marecl/Temperature-Station/Temperature-Station_DS3231/PCB/TermometryWiFi_MainBoard_57640_etch_silk_bottom.pdf

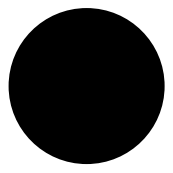
[picture p11: page 1]
