marecl/Temperature-Station/Temperature-Station_DS3231/PCB/TermometryWiFi_MainBoard_57640_etch_silk_bottom_mirror.pdf

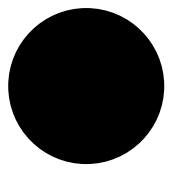
[picture p12: page 1]
