marecl/Temperature-Station/Temperature-Station_DS3231/PCB/TermometryWiFi_MainBoard_57640_etch_silk_top.pdf

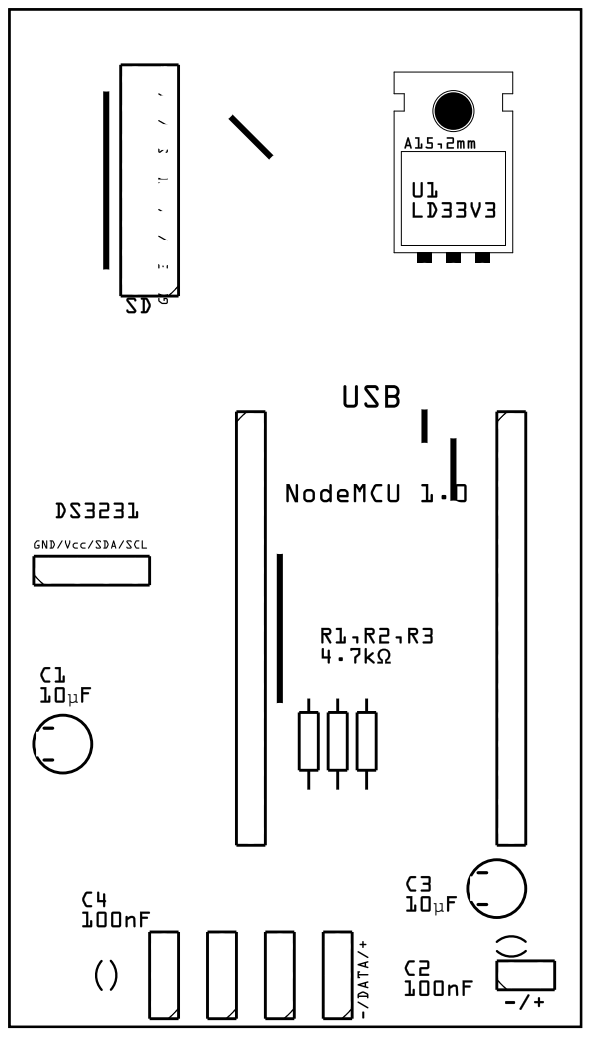
[picture p13: page 1]
