marecl/Temperature-Station/Temperature-Station_DS3231/PCB/TermometryWiFi_MainBoard_57640_etch_silk_top_mirror.pdf

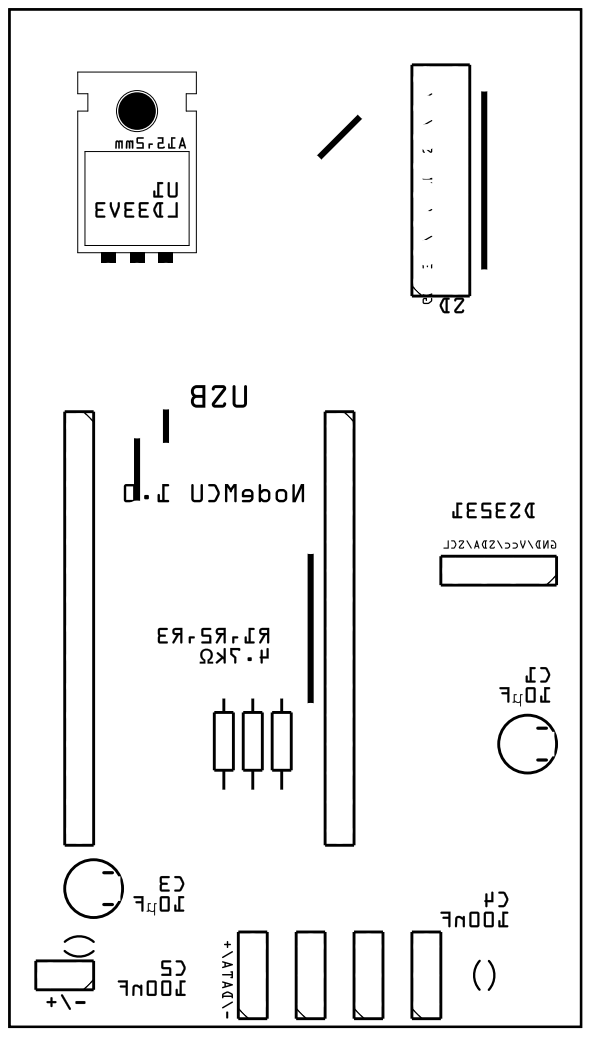
[picture p14: page 1]
