marecl/Temperature-Station/Temperature-Station_PCF8563_JSON/Czas/Czas.cpp

#include "Czas.h"

/* PCF8563 inferfacing library */

Czas::Czas(byte sda_pin, byte scl_pin) {
  dls = true;
  Wire.begin(sda_pin, scl_pin);
  Wire.beginTransmission(RTC_ADDR);
  Wire.write(0x0D);
  Wire.write(0x00); //disable clock output
  Wire.endTransmission();
}

Czas::~Czas() {
}

byte Czas::bcdToDec(byte value) {
  return ((value / 16) * 10 + value % 16);
}

byte Czas::decToBcd(byte value) {
  return (value / 10 * 16 + value % 10);
}

void Czas::readRTC() {
  Wire.beginTransmission(RTC_ADDR);
  Wire.write(0x02);
  Wire.endTransmission();
  Wire.requestFrom(RTC_ADDR, 7);
  this->second = this->bcdToDec(Wire.read() & B01111111); // sek
  this->minute = this->bcdToDec(Wire.read() & B01111111); // min
  this->hour = this->bcdToDec(Wire.read() & B00111111); //godz
  this->day = this->bcdToDec(Wire.read() & B00111111); //dz msc
  this->dow = this->bcdToDec(Wire.read() & B00000111); //dz tyg
  this->month = this->bcdToDec(Wire.read() & B00011111); // msc
  this->year = this->bcdToDec(Wire.read()); //rok
  this->year += 2000;
}

void Czas::setRTC(uint32_t t) {
  t -= 946684800UL;
  t = t + (3600 * timezone);
  if (this->dls) t += 3600;
  uint8_t ss = t % 60;
  t /= 60;
  uint8_t mm = t % 60;
  t /= 60;
  uint8_t hh = t % 24;
  uint16_t d = t / 24;
  int dt = (d % 7) - 1;
  uint8_t przest = 0;
  uint8_t r;
  uint8_t m;
  for (r = 0; ; ++r) {
    przest = r % 4 == 0;
    if (d < 365 + przest) break;
    d -= 365 + przest;
  }
  for (m = 1; ; m++) {
    uint8_t dniwmsc = pgm_read_byte(daysInMonth + m - 1);
    if (przest && m == 2)
      dniwmsc++;
    if (d < dniwmsc)
      break;
    d -= dniwmsc;
  }
  d++;

  Wire.beginTransmission(RTC_ADDR);
  Wire.write(0x02);
  Wire.write(this->decToBcd(ss)); //sek
  Wire.write(this->decToBcd(mm)); //min
  Wire.write(this->decToBcd(hh)); //godz
  Wire.write(this->decToBcd(d)); //dzien
  Wire.write(this->decToBcd(dt)); //dzien tyg (1-7)
  Wire.write(this->decToBcd(m)); //msc
  Wire.write(this->decToBcd(r)); //rok-2000
  Wire.endTransmission();
}

void Czas::setRTC(uint8_t ss, uint8_t mm, uint8_t hh, uint16_t d, uint8_t dt, uint8_t m, uint8_t r) {
  Wire.beginTransmission(RTC_ADDR);
  Wire.write(0x02);
  Wire.write(this->decToBcd(ss)); //sek
  Wire.write(this->decToBcd(mm)); //min
  Wire.write(this->decToBcd(hh)); //godz
  Wire.write(this->decToBcd(d)); //dzien
  Wire.write(this->decToBcd(dt)); //dzien tyg (1-7)
  Wire.write(this->decToBcd(m)); //msc
  Wire.write(this->decToBcd(r - 2000)); //rok-2000
  Wire.endTransmission();
}

uint32_t Czas::DateToEpoch(uint8_t ss, uint8_t mm, uint8_t hh, uint16_t d, uint8_t dt, uint8_t m, uint8_t r) {
  Serial.println("Not implemented yet");
  return 0;
}

bool Czas::CompareTimeEpoch(uint32_t t, int tolerance) { //tolerance in seconds, less than 1 minute
  t -= 946684800UL;
  t = t + (3600 * timezone);
  if (this->dls) t += 3600;
  uint8_t ss = t % 60;
  t /= 60;
  uint8_t mm = t % 60;
  t /= 60;
  uint8_t hh = t % 24;
  uint16_t d = t / 24;
  uint8_t przest = 0;
  uint8_t r;
  uint8_t m;
  for (r = 0; ; ++r) {
    przest = r % 4 == 0;
    if (d < 365 + przest) break;
    d -= 365 + przest;
  }
  for (m = 1; ; m++) {
    uint8_t dniwmsc = pgm_read_byte(daysInMonth + m - 1);
    if (przest && m == 2)
      dniwmsc++;
    if (d < dniwmsc)
      break;
    d -= dniwmsc;
  }
  d++;
  
  if (r != (this-> year - 2000)) return false;
  if (m != this->month) return false;
  if (d != this->day) return false;
  if (hh != this->hour) return false;
  if (mm != this->minute) return false;
  if (ss < (this->second - tolerance)) return false;
  if (ss > (this->second + tolerance)) return false;
  return true;
}
